OWongit/DAQ_Hardware/DAQ symbols and footprints/VJ0603Y104JXXAC/VJ0603Y104JXXAC.step

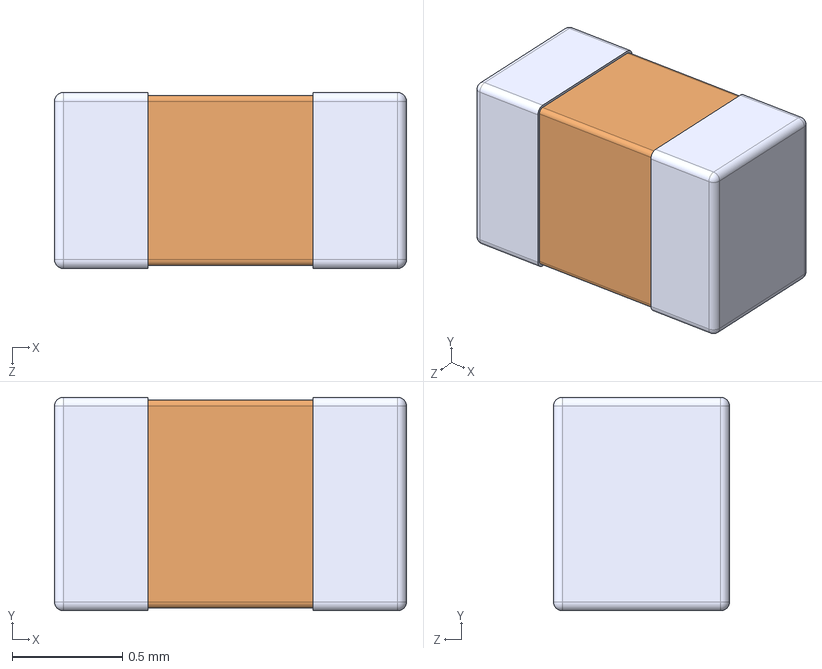
[picture p20: CAD file, 2026-01-15]
DAQ symbols and footprints/VJ0603Y104JXXAC/VJ0603Y104JXXAC.step
1.60 x 0.97 x 0.8 mm
